PrakashHamirwasia/WeatherSync/Images/2.jpeg

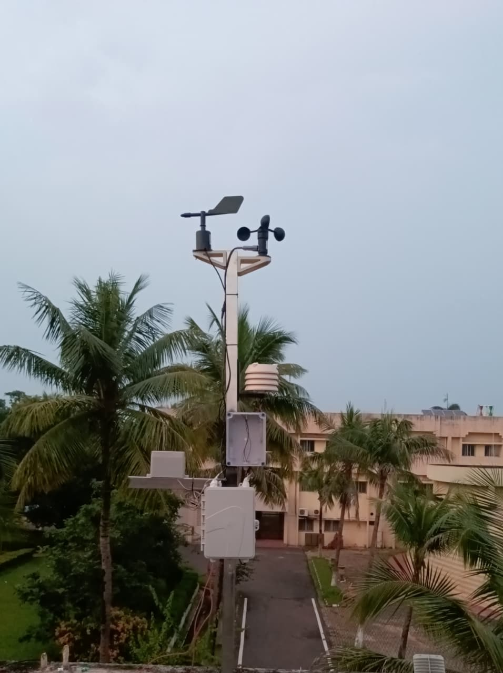
Images/2.jpeg
